chubertbuilds/astrolabe_esp32/docs/20260702_181357.jpg

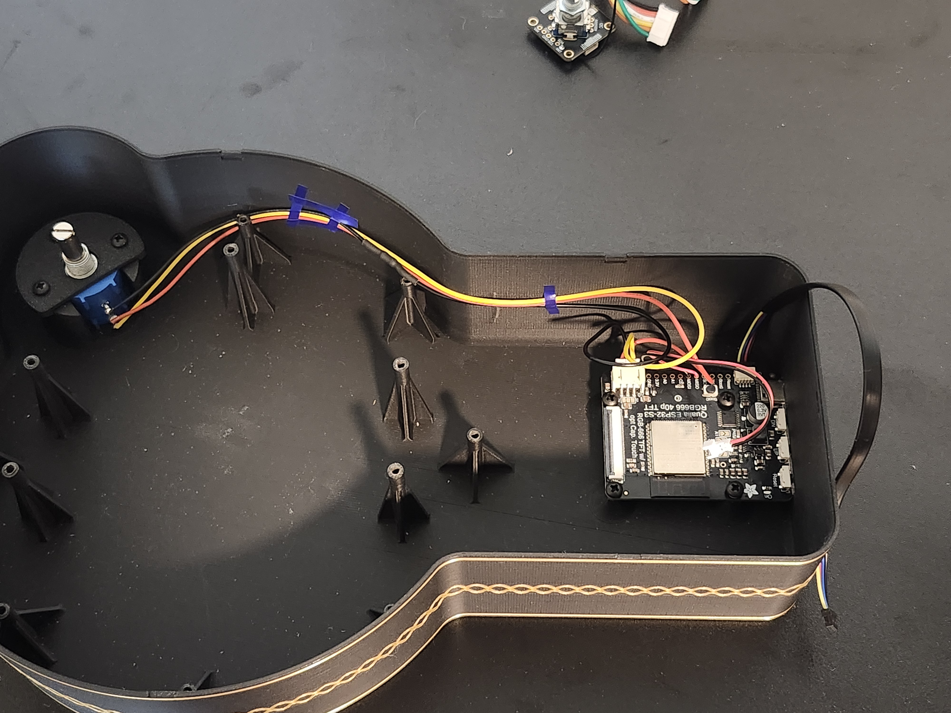
docs/20260702_181357.jpg
