chubertbuilds/astrolabe_esp32/src/Ephemerides.cpp

#include "src/Ephemerides.h"
static SphereVector transformRectToEcliptic(RectVector p);
static SphereVector transformRectToEquatorial(RectVector p);
static RectVector rotateVectorEclToEqu(RectVector p);

static double earth_x(double t);
static double earth_y(double t);
static double earth_z(double t);

static double emb_x(double t);
static double emb_y(double t);
static double emb_z(double t);

static double jupiter_x(double t);
static double jupiter_y(double t);
static double jupiter_z(double t);

static double mars_x(double t);
static double mars_y(double t);
static double mars_z(double t);

static double mercury_x(double t);
static double mercury_y(double t);
static double mercury_z(double t);

static double saturn_x(double t);
static double saturn_y(double t);
static double saturn_z(double t);

static double venus_x(double t);
static double venus_y(double t);
static double venus_z(double t);

PlanetData getPlanetData(double jd) {
    double t=(jd - 2451545.0) / 365250.0; //from https://celestialprogramming.com/vsop87-multilang/index.html
    RectVector earth_position_sun = {.x = earth_x(t), .y = earth_y(t), .z = earth_z(t)};
    RectVector emb_position_sun = {.x = emb_x(t), .y = emb_y(t), .z = emb_z(t)};
    RectVector mercury_position_sun = {.x = mercury_x(t), .y = mercury_y(t), .z = mercury_z(t)};
    RectVector venus_position_sun = {.x = venus_x(t), .y = venus_y(t), .z = venus_z(t)};
    RectVector mars_position_sun = {.x = mars_x(t), .y = mars_y(t), .z = mars_z(t)};
    RectVector jupiter_position_sun = {.x = jupiter_x(t), .y = jupiter_y(t), .z = jupiter_z(t)};
    RectVector saturn_position_sun = {.x = saturn_x(t), .y = saturn_y(t), .z = saturn_z(t)};

    RectVector sun_position_earth = getNegativeVector(earth_position_sun);
    RectVector emb_position_earth = addVectors(emb_position_sun, sun_position_earth);
    RectVector mercury_position_earth = addVectors(mercury_position_sun, sun_position_earth);
    RectVector venus_position_earth = addVectors(venus_position_sun, sun_position_earth);
    RectVector mars_position_earth = addVectors(mars_position_sun, sun_position_earth);
    RectVector jupiter_position_earth = addVectors(jupiter_position_sun, sun_position_earth);
    RectVector saturn_position_earth = addVectors(saturn_position_sun, sun_position_earth);


    PlanetData data = {
        .sun_ecl_latlong = transformRectToEcliptic(sun_position_earth), 
        .moon_ecl_latlong = transformRectToEcliptic(emb_position_earth),
        .mercury_ecl_latlong = transformRectToEcliptic(mercury_position_earth),
        .venus_ecl_latlong = transformRectToEcliptic(venus_position_earth),
        .mars_ecl_latlong = transformRectToEcliptic(mars_position_earth),
        .jupiter_ecl_latlong = transformRectToEcliptic(jupiter_position_earth),
        .saturn_ecl_latlong = transformRectToEcliptic(saturn_position_earth),
        .sun_equ_latlong = transformRectToEquatorial(sun_position_earth),
        .moon_equ_latlong = transformRectToEquatorial(emb_position_earth),
        .mercury_equ_latlong = transformRectToEquatorial(mercury_position_earth),
        .venus_equ_latlong = transformRectToEquatorial(venus_position_earth),
        .mars_equ_latlong = transformRectToEquatorial(mars_position_earth),
        .jupiter_equ_latlong = transformRectToEquatorial(jupiter_position_earth),
        .saturn_equ_latlong = transformRectToEquatorial(saturn_position_earth)
    };

    return data;
}

static SphereVector transformRectToEcliptic(RectVector p) {
    return getLatLongFromRect(p);
}

static SphereVector transformRectToEquatorial(RectVector p) {
    RectVector p_equ = rotateVectorEclToEqu(p);
    return getLatLongFromRect(p_equ);

}

static RectVector rotateVectorEclToEqu(RectVector p) {
   return rotateVectorAboutX(p, e);
}

//earth and emb are from vsop87a_small
//jupiter and saturn are from vsop87a_nano
//mercury, venus, and mars are from vsop87a_micro


static double earth_x(double t){
   double earth_x_0=0.0;
   earth_x_0+=     0.99982928844 * cos( 1.75348568475 +     6283.07584999140*t);
   earth_x_0+=     0.00835257300 * cos( 1.71034539450 +    12566.15169998280*t);
   earth_x_0+=     0.00561144206 * cos( 0.00000000000 +        0.00000000000*t);
   earth_x_0+=     0.00010466628 * cos( 1.66722645223 +    18849.22754997420*t);
   earth_x_0+=     0.00003110838 * cos( 0.66875185215 +    83996.84731811189*t);
   earth_x_0+=     0.00002552498 * cos( 0.58310207301 +      529.69096509460*t);
   earth_x_0+=     0.00002137256 * cos( 1.09235189672 +     1577.34354244780*t);
   earth_x_0+=     0.00001709103 * cos( 0.49540223397 +     6279.55273164240*t);
   earth_x_0+=     0.00001707882 * cos( 6.15315547484 +     6286.59896834040*t);
   earth_x_0+=     0.00001445242 * cos( 3.47272783760 +     2352.86615377180*t);
   earth_x_0+=     0.00001091006 * cos( 3.68984782465 +     5223.69391980220*t);
   earth_x_0+=     0.00000934429 * cos( 6.07389922585 +    12036.46073488820*t);
   earth_x_0+=     0.00000899144 * cos( 3.17571950523 +    10213.28554621100*t);
   earth_x_0+=     0.00000566514 * cos( 2.15262034016 +     1059.38193018920*t);
   earth_x_0+=     0.00000684416 * cos( 1.30699021227 +     5753.38488489680*t);
   earth_x_0+=     0.00000734455 * cos( 4.35500196530 +      398.14900340820*t);
   earth_x_0+=     0.00000681437 * cos( 2.21821534685 +     4705.73230754360*t);
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
   saturn_z_0+=     0.01214249867 * cos( 0.00000000000 +        0.00000000000*t);
   saturn_z_0+=     0.00329280791 * cos( 0.57121407104 +      206.18554843720*t);
   saturn_z_0+=     0.00286934048 * cos( 3.48073526693 +      220.41264243880*t);

   double saturn_z_1=0.0;
   saturn_z_1+=     0.01906503283 * cos( 4.94544746116 +      213.29909543800*t);
   saturn_z_1+=     0.00528301265 * cos( 3.14159265359 +        0.00000000000*t);
   saturn_z_1+=     0.00130262284 * cos( 2.26140980879 +      206.18554843720*t);
   saturn_z_1+=     0.00101466332 * cos( 1.79095829545 +      220.41264243880*t);
   saturn_z_1=saturn_z_1 * t;

   double saturn_z_2=0.0;
   saturn_z_2+=     0.00131275155 * cos( 0.08868998101 +      213.29909543800*t);
   saturn_z_2=saturn_z_2 * t * t;

   return saturn_z_0+saturn_z_1+saturn_z_2;
}
