chubertbuilds/astrolabe_esp32/src/StarChart.h

#pragma once

#include <array>
#include "src/CircleMath.h"

constexpr std::array<SphereVector, 12> fixed_star_data = {
SphereVector{.lat = 0.7148, .lon = 0.8210},
SphereVector{.lat = -0.1431, .lon = 1.3724},
SphereVector{.lat = 0.8028, .lon = 1.3818},
SphereVector{.lat = 0.1293, .lon = 1.5497},
SphereVector{.lat = -0.2917, .lon = 1.7678},
SphereVector{.lat = 0.0912, .lon = 2.0041},
SphereVector{.lat = 1.0778, .lon = 2.8961},
SphereVector{.lat = 0.8607, .lon = 3.6108},
SphereVector{.lat = 0.3349, .lon = 3.7336},
SphereVector{.lat = 0.6769, .lon = 4.8736},
SphereVector{.lat = 0.1548, .lon = 5.1957},
SphereVector{.lat = 0.7903, .lon = 5.4168}
};

std::array<std::array<float, 3>, 272> star_data = {{
{0.03659155498858278, 0.5879778080944164, 13.880887006294472},
{0.30425452185391144, 0.513700388707582, 13.880887006294472},
{0.5406099180410702, 0.44178389242516647, 13.683995802785692},
{0.17159495429190919, 0.5673726000846419, 6.343966522124878},
{0.18648188559089915, 0.4528913536810162, 5.346526815770006},
{0.4275693057125275, 0.37758431718214985, 4.486086109345916},
{6.029767135892618, 0.441824453569084, 4.316433727144539},
{5.635487804000318, 1.1022888448282995, 8.584361228657889},
{5.7848232653446034, 1.0055977830776754, 8.276590291205082},
{5.998045049517098, 1.3227347920260206, 6.343966522124878},
{5.885381137418778, 1.000350096754478, 4.147646825878929},
{6.062601869666284, 1.4597108154213059, 3.979751311919144},
{5.989159869183404, 1.1418819077719098, 3.7019823027357934},
{5.195749190078259, 0.8560840773546672, 22.791470511042352},
{5.176033514515418, 0.8300202791196916, 9.704049585062508},
{4.997794673537584, 0.7832025820478773, 8.031441377245525},
{5.2853122150853915, 1.0144411667263094, 6.522230323115297},
{5.085434927485436, 0.9470659703300557, 5.813137336550644},
{5.001455501643641, 1.08906126918766, 5.404572519715196},
{5.215536133252223, 0.8939784480250919, 3.8127748414081046},
{0.5548903474249922, 0.6560932789952623, 14.27576050575282},
{0.5002077275189665, 0.6897468246283364, 10.207276755294693},
{0.741691482824902, 0.6096748390575274, 4.372889588868012},
{1.3818135298299938, 0.4040360950518189, 27.618851444966296},
{1.5687433832622382, 0.4147509873588355, 15.003388479370416},
{1.5695775052005871, 0.4962653342495484, 10.333597249883935},
{1.2958793352259663, 0.5410799268689476, 9.892370312411314},
{1.3175875950181677, 0.4262957862171125, 7.7872647371805925},
{1.33742180752604, 0.45325568599802013, 6.880658843672994},
{1.319809253711852, 0.45492669976749844, 3.9239889528489167},
{1.5687273844107619, 0.32217251466193303, 3.7573253050949544},
{3.733575610942795, 0.7108301158308418, 28.555062199270104},
{3.861486428498329, 0.6119108651960095, 12.057970950231704},
{3.64200182119326, 0.7212415398901312, 9.955248391995678},
{3.8614827923957216, 0.6119108651960095, 9.829544320391573},
{3.8051639263159514, 0.4844109428742045, 7.726375100752189},
{3.9946295977072386, 0.5394004734987965, 5.230682321453905},
{3.9354840254597585, 0.46216400604327845, 5.057543003374415},
{3.804080367738671, 0.5730399170728102, 4.599656448853059},
{2.1664590199875198, 0.851282412410008, 4.827891470635125},
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
}};
