chubertbuilds/astrolabe_esp32/src/CalibrationPoints.h

std::vector<float> calibration_points = {
  0,
  166.3,
  333.4,
  496.9,
  666.8,
  831.4,
  994.7,
  1166.2,
  1338.3,
  1512.2,
  1684.3,
  1859.1,
  2024.0,
  2186.3,
  2338.7,
  2480.3,
  2614.4,
  2737.2,
  2851.8,
  2956.4,
  3056.0,
  3156.3,
  3244.9,
  3334.6,
  3422.9,
  3505.7,
  3594.6,
  3679.9,
  3759.0,
  3842.7,
  3929.3,
  4013.5
};
