chubertbuilds/astrolabe_esp32/docs/20260702_185457.jpg

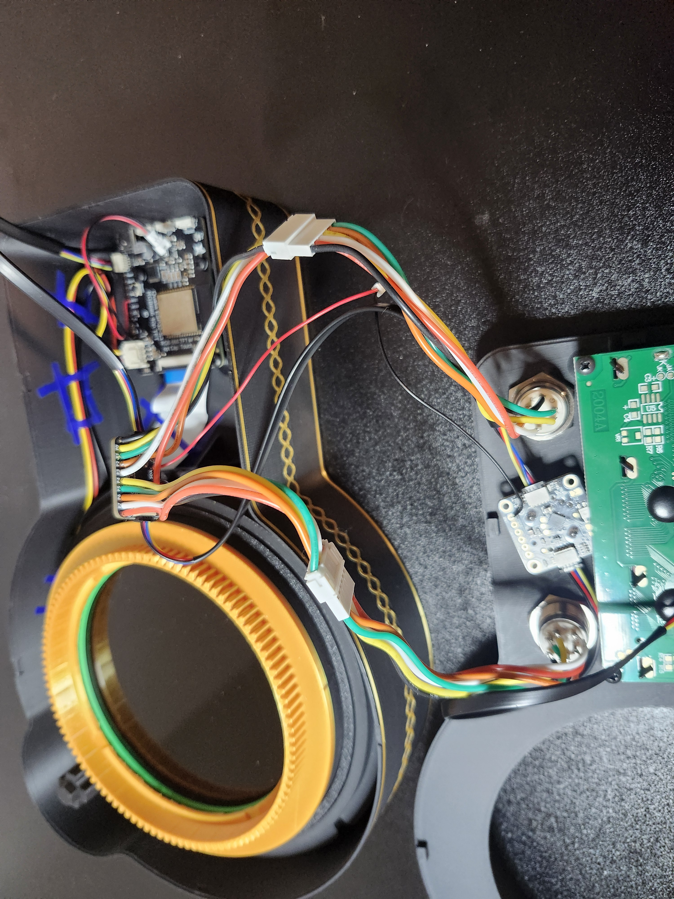
docs/20260702_185457.jpg
